xrstf/froy/include/rtc.h

#pragma once

#include "config.h"
#include <MCP7940NRTC.h>
#include <TimeLib.h>

namespace rtc {
	extern MCP7940NRTC rtc;

	uint8_t encodeYear(uint16_t year);
	uint16_t decodeYear(uint8_t year);

	bool exists();
	bool isConfigured();
	bool read(tmElements_t &tm);
	bool set(tmElements_t &tm);
	void printToSerial(tmElements_t &tm);
} // namespace rtc
